rfsparkling/RPi_ISM/datasheet/buzzer/KDMG10008C-03 - KINGSTATE - LOUDSPEAKER, MICRO, 10MM _ Farnell element14_files/129988006-40.jpg

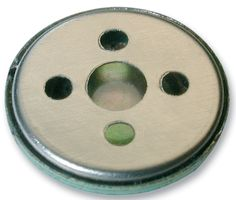
datasheet/buzzer/KDMG10008C-03 - KINGSTATE - LOUDSPEAKER, MICRO, 10MM _ Farnell element14_files/129988006-40.jpg
