rfsparkling/RPi_ISM/datasheet/pinhead_connector/CLH-115-F-D-DV - SAMTEC - Board-To-Board Connector, CLH Series, Surface Mount, Receptacle, 30, 2.54 mm, Gold Plated Contacts _ Farnell element14_files/1927779-40.jpg

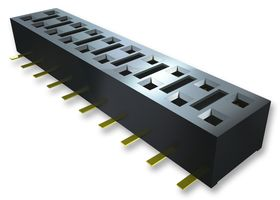
datasheet/pinhead_connector/CLH-115-F-D-DV - SAMTEC - Board-To-Board Connector, CLH Series, Surface Mount, Receptacle, 30, 2.54 mm, Gold Plated Contacts _ Farnell element14_files/1927779-40.jpg
