rfsparkling/RPi_ISM/datasheet/RPi_ISM_interfacing/Raspberry Pi SPI and I2C Tutorial - learn.sparkfun.com_files/i2c-0.jpg

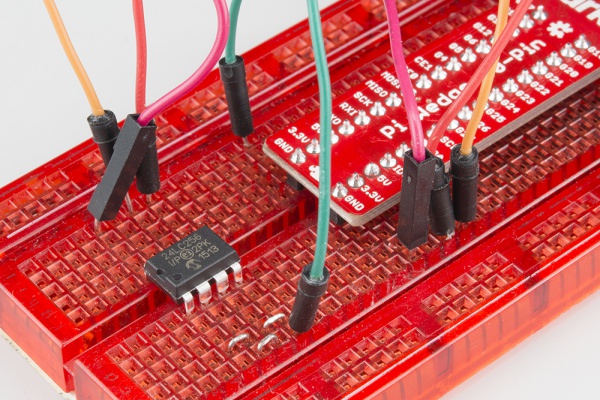
datasheet/RPi_ISM_interfacing/Raspberry Pi SPI and I2C Tutorial - learn.sparkfun.com_files/i2c-0.jpg
