rfsparkling/RPi_ISM/datasheet/RPi_ISM_interfacing/Raspberry Pi SPI and I2C Tutorial - learn.sparkfun.com_files/pin-labels-on-pi.png

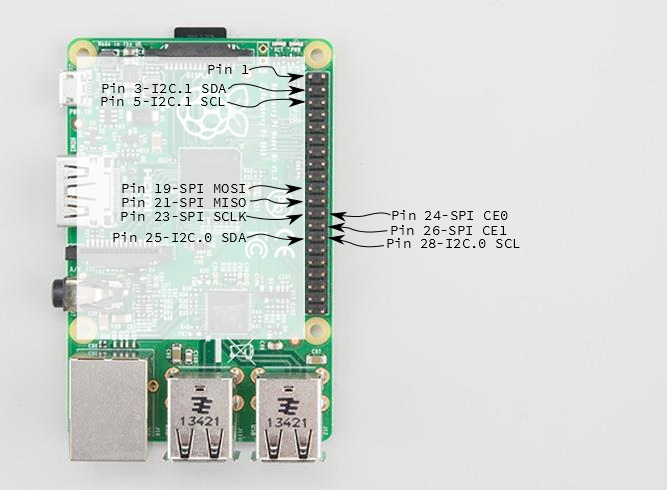
datasheet/RPi_ISM_interfacing/Raspberry Pi SPI and I2C Tutorial - learn.sparkfun.com_files/pin-labels-on-pi.png
