rfsparkling/RPi_ISM/datasheet/RPi_ISM_interfacing/Raspberry Pi SPI and I2C Tutorial - learn.sparkfun.com_files/wedge-n-pi.jpg

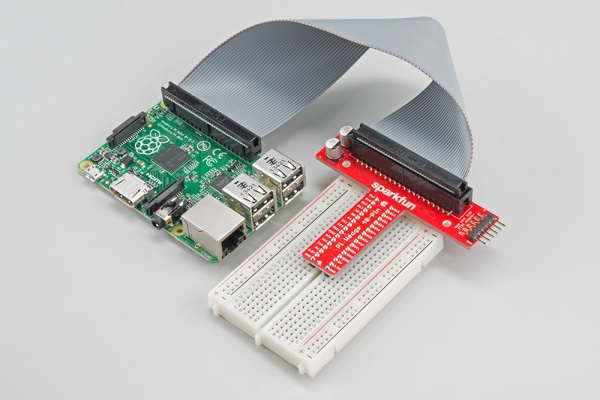
datasheet/RPi_ISM_interfacing/Raspberry Pi SPI and I2C Tutorial - learn.sparkfun.com_files/wedge-n-pi.jpg
